0xe1f/red/3dprint/stl/led_connector_2x1_short.stl

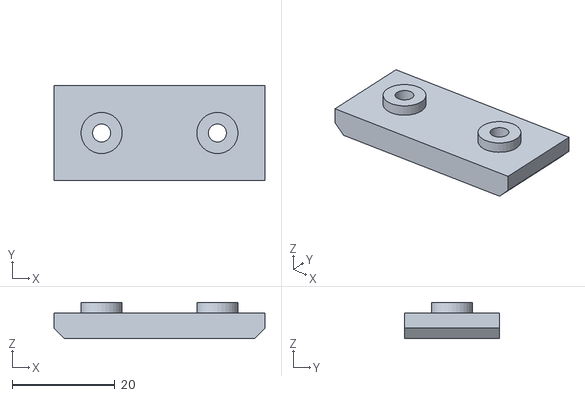
[picture p23: CAD file, 2024-03-31]
3dprint/stl/led_connector_2x1_short.stl
41.0 x 18.5 x 7.00
