0xe1f/red/3dprint/stl/ribbon_cable_clip.stl

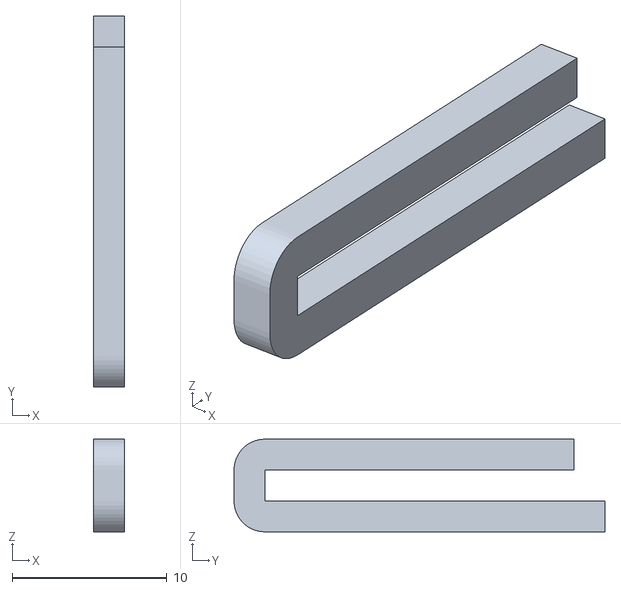
[picture p24: CAD file, 2024-03-31]
3dprint/stl/ribbon_cable_clip.stl
2.00 x 24.0 x 6.00
