0xe1f/red/pubsub/files.c

// Copyright (c) 2024 Akop Karapetyan
//
// Licensed under the Apache License, Version 2.0 (the "License");
// you may not use this file except in compliance with the License.
// You may obtain a copy of the License at
//
//    http://www.apache.org/licenses/LICENSE-2.0
//
// Unless required by applicable law or agreed to in writing, software
// distributed under the License is distributed on an "AS IS" BASIS,
// WITHOUT WARRANTIES OR CONDITIONS OF ANY KIND, either express or implied.
// See the License for the specific language governing permissions and
// limitations under the License.

#include <stdio.h>
#include <stdlib.h>
#include <string.h>
#include <sys/stat.h>
#include <unistd.h>
#include "unzip.h"
#include "un7z.h"
#include "libretro.h"
#include "server_args.h"
#include "log.h"
#include "files.h"

#define LOG_TAG "files"

static const char *preload_blocklist = "iso|cue|mp3|chd";
static const char *system_path_name = "bios";
static const char *save_path_name = "save";
static const char *recording_path_name = "rec";
static char system_path[1024];
static char save_path[1024];
static char recording_path[1024];
static char extracted_tempfile[1024] = {0};
static const char* get_filename(const char *path, bool include_ext);

extern struct retro_system_info system_info;
extern const struct retro_system_content_info_override *content_info;
extern struct retro_game_info *game_info;
extern struct retro_game_info_ext *game_info_ext;
extern ArgsOptions args;

static bool is_path_supported(const char *path, bool *need_fullpath);
static bool has_extension(const char *path, const char *ext);
static bool load_zip(const char *path);
static bool load_7z(const char *path);
static bool load_direct(const char *path);
static bool extension_one_of(const char *ext, const char *ext_delim);
static void copy_str(char *dst, size_t dst_size, const char *src);
static void copy_str_n(char *dst, size_t dst_size, const char *src, size_t n);
static void append_str(char *dst, size_t dst_size, const char *src);
static void join_dir(char *dst, size_t dst_size, const char *base, const char *name);
static void dirname_copy(char *dst, size_t dst_size, const char *path);
static void split_name_ext(const char *path, char *name, size_t name_size,
                           char *ext, size_t ext_size);

static void copy_str(char *dst, size_t dst_size, const char *src)
{
    if (dst_size == 0) {
        return;
    }
    if (!src) {
        dst[0] = '\0';
        return;
    }
    size_t n = strlen(src);
    if (n >= dst_size) {
        n = dst_size - 1;
    }
    memcpy(dst, src, n);
    dst[n] = '\0';
}

static void copy_str_n(char *dst, size_t dst_size, const char *src, size_t n)
{
    if (dst_size == 0) {
        return;
    }
    if (!src) {
        dst[0] = '\0';
        return;
    }
    size_t len = 0;
    while (len < n && src[len]) {
        len++;
    }
    if (len >= dst_size) {
        len = dst_size - 1;
    }
    memcpy(dst, src, len);
    dst[len] = '\0';
}

static void append_str(char *dst, size_t dst_size, const char *src)
{
    size_t used = strlen(dst);
    if (used < dst_size) {
        copy_str(dst + used, dst_size - used, src);
    }
}

static void join_dir(char *dst, size_t dst_size, const char *base, const char *name)
{
    size_t len = strlen(base);
    copy_str(dst, dst_size, base);
    if (len > 0 && base[len - 1] != '/') {
        append_str(dst, dst_size, "/");
    }
    append_str(dst, dst_size, name);
}

static void dirname_copy(char *dst, size_t dst_size, const char *path)
{
    const char *slash = strrchr(path, '/');
    if (slash) {
        copy_str_n(dst, dst_size, path, (size_t)(slash - path));
    } else {
        copy_str(dst, dst_size, ".");
    }
}

static void split_name_ext(const char *path, char *name, size_t name_size,
                           char *ext, size_t ext_size)
{
    const char *slash = strrchr(path, '/');
    copy_str(name, name_size, slash ? slash + 1 : path);
    ext[0] = '\0';
    char *dot = strrchr(name, '.');
    if (dot) {
        copy_str(ext, ext_size, dot + 1);
        *dot = '\0';
    }
}

static bool extension_one_of(const char *ext, const char *ext_delim)
{
    for (const char *p = ext_delim; *p; p++) {
        if (strncmp(p, ext, strlen(ext)) == 0 &&
            (*(p + strlen(ext)) == '|' || *(p + strlen(ext)) == '\0')) {
            return true;
        }
        // skip to next extension after pipe
        while (*p && *p != '|') p++;
    }
    return false;
}

static bool is_path_supported(const char *path, bool *need_fullpath)
{
    *need_fullpath = false;
    const char *ext = strrchr(path, '.');
    if (!ext) {
        log_w(LOG_TAG, "No file extension found: %s\n", path);
        return false;
    }
    ext++; // skip the dot

    for (const struct retro_system_content_info_override *info = content_info; info && info->extensions; info++) {
        if (extension_one_of(ext, info->extensions)) {
            *need_fullpath = info->need_fullpath;
            return true;
        }
    }

    if (system_info.valid_extensions && extension_one_of(ext, system_info.valid_extensions)) {
        *need_fullpath = system_info.need_fullpath;
        return true;
    }

    return false;
}

static bool has_extension(const char *path, const char *ext)
{
    const char *file_ext = strrchr(path, '.');
    return file_ext && strcasecmp(file_ext + 1, ext) == 0;
}

static bool load_zip(const char *path)
{
    static struct retro_game_info info_local;
    static struct retro_game_info_ext info_local_ext;
    info_local = (struct retro_game_info){ 0 };
    info_local_ext = (struct retro_game_info_ext){ 0 };
    extracted_tempfile[0] = '\0';

    unzFile fd = unzOpen(path);
    if (!fd) {
        log_e(LOG_TAG, "Failed to open zip: %s\n", path);
        return false;
    }

    static char archived_path[1024];
    static char archived_filename[512];
    static char archived_ext[512];
    static char dir[1024];
    void *data = NULL;
    archived_path[0] = '\0';
    archived_filename[0] = '\0';
    archived_ext[0] = '\0';
    dirname_copy(dir, sizeof(dir), path);

    unz_file_info info;
    bool need_fullpath = false;
    int ret = unzGoToFirstFile(fd);
    while (ret == UNZ_OK) {
        if (unzGetCurrentFileInfo(fd, &info, archived_path, sizeof(archived_path), 0, 0, 0, 0) == UNZ_OK) {
            if (is_path_supported(archived_path, &need_fullpath)) {
                if ((ret = unzOpenCurrentFile(fd)) == UNZ_OK) {
                    size_t size = info.uncompressed_size;
                    if (!(data = malloc(size))) {
                        log_e(LOG_TAG, "Failed to allocate %zu bytes for %s\n", size, archived_path);
                        unzCloseCurrentFile(fd);
                        continue;
                    }

                    if ((ret = unzReadCurrentFile(fd, data, size)) == (int) size) {
                        log_i(LOG_TAG, "Loaded '%s'\n", archived_path);

                        split_name_ext(archived_path, archived_filename, sizeof(archived_filename),
                                       archived_ext, sizeof(archived_ext));

                        if (need_fullpath) {
                            // Core needs a real file path - extract to a temp file
                            copy_str(extracted_tempfile, sizeof(extracted_tempfile), save_path);
                            append_str(extracted_tempfile, sizeof(extracted_tempfile), "/rom_XXXXXX");
                            int tmp_fd = mkstemp(extracted_tempfile);
                            FILE *tf = tmp_fd != -1 ? fdopen(tmp_fd, "wb") : NULL;
                            if (!tf) {
                                log_e(LOG_TAG, "Failed to create temp file in %s\n", save_path);
                                if (tmp_fd != -1) { close(tmp_fd); unlink(extracted_tempfile); }
                                extracted_tempfile[0] = '\0';
                                free(data);
                                data = NULL;
                                unzCloseCurrentFile(fd);
                                break;
                            }
                            fwrite(data, 1, size, tf);
                            fclose(tf);
                            free(data);
                            data = NULL;
                            size = 0;
                            info_local = (struct retro_game_info){ extracted_tempfile, NULL, 0, NULL };
                            info_local_ext = (struct retro_game_info_ext){
                                /* full_path */ extracted_tempfile,
                                /* archive_path */ path,
                                /* archive_file */ archived_path,
                                /* dir */ dir,
                                /* name */ archived_filename,
                                /* ext */ archived_ext,
                                /* meta */ NULL,
                                /* data */ NULL,
                                /* size */ 0,
                                /* file_in_archive */ true,
                                /* persistent_data */ true
                            };
                        } else {
                            info_local = (struct retro_game_info){ path, data, size, NULL };
                            info_local_ext = (struct retro_game_info_ext){
                                /* full_path */ NULL,
                                /* archive_path */ path,
                                /* archive_file */ archived_path,
                                /* dir */ dir,
                                /* name */ archived_filename,
                                /* ext */ archived_ext,
                                /* meta */ NULL,
                                /* data */ data,
                                /* size */ size,
                                /* file_in_archive */ true,
                                /* persistent_data */ true
                            };
                        }

                        unzCloseCurrentFile(fd);
                        break;
                    }

                    free(data);
                    unzCloseCurrentFile(fd);
                }
            }
        }
        ret = unzGoToNextFile(fd);
    }
    unzClose(fd);

    if (need_fullpath ? !(*extracted_tempfile) : !info_local.data) {
        log_w(LOG_TAG, "Nothing loaded from archive: %s\n", path);
        return false;
    }

    game_info = &info_local;
    game_info_ext = &info_local_ext;

    return true;
}

static bool load_7z(const char *path)
{
    static struct retro_game_info info_local;
    static struct retro_game_info_ext info_local_ext;
    info_local = (struct retro_game_info){ 0 };
    info_local_ext = (struct retro_game_info_ext){ 0 };
    extracted_tempfile[0] = '\0';

    _7z_file *z7 = NULL;
    _7z_error z7_err;

    z7_err = _7z_file_open(path, &z7);
    if (z7_err != _7ZERR_NONE) {
        return false;
    }

    static char archived_path[1024];
    static char archived_filename[512];
    static char archived_ext[512];
    static char dir[1024];
    archived_path[0] = '\0';
    archived_filename[0] = '\0';
    archived_ext[0] = '\0';
    dirname_copy(dir, sizeof(dir), path);

    unsigned short name_utf16[2048];
    bool need_fullpath = false;

    for (int i = 0, n = z7->db.NumFiles; i < n; i++) {
        size_t len = SzArEx_GetFileNameUtf16(&z7->db, i, NULL);
        size_t utf16_cap = sizeof(name_utf16) / sizeof(name_utf16[0]);
        if (len > utf16_cap) {
            log_e(LOG_TAG, "File name at index %d too long (%zu chars)\n", i, len);
            continue;
        }

        SzArEx_GetFileNameUtf16(&z7->db, i, name_utf16);
        size_t out = 0;
        size_t max = sizeof(archived_path) - 1;
        for (size_t j = 0; j < len && out < max; j++) {
            archived_path[out++] = (char)(name_utf16[j] & 0xff);
        }
        archived_path[out] = '\0';

        if (is_path_supported(archived_path, &need_fullpath)) {
            unsigned long size = SzArEx_GetFileSize(&z7->db, i);
            void *data = malloc(size);
            if (!data) {
                log_e(LOG_TAG, "Failed to allocate %zu bytes for %s\n", size, archived_path);
                continue;
            }

            z7->curr_file_idx = i;
            unsigned int wrote = 0;

            z7_err = _7z_file_decompress(z7, data, size, &wrote);
            if (z7_err != _7ZERR_NONE) {
                free(data);
                log_e(LOG_TAG, "Failed to decompress '%s' (err: %d)\n", archived_path, z7_err);
                continue;
            }

            unsigned int crc = crc32(0, (unsigned char *) data, wrote);
            if (crc != z7->db.CRCs.Vals[i]) {
                free(data);
                log_e(LOG_TAG, "CRC mismatch for '%s' (expected: %08x, got: %08x)\n",
                    archived_path, z7->db.CRCs.Vals[i], crc);
                continue;
            }

            split_name_ext(archived_path, archived_filename, sizeof(archived_filename),
                           archived_ext, sizeof(archived_ext));

            if (need_fullpath) {
                // Core needs a real file path - extract to a temp file
                copy_str(extracted_tempfile, sizeof(extracted_tempfile), save_path);
                append_str(extracted_tempfile, sizeof(extracted_tempfile), "/rom_XXXXXX");
                int tmp_fd = mkstemp(extracted_tempfile);
                FILE *tf = tmp_fd != -1 ? fdopen(tmp_fd, "wb") : NULL;
                if (!tf) {
                    log_e(LOG_TAG, "Failed to create temp file in %s\n", save_path);
                    if (tmp_fd != -1) { close(tmp_fd); unlink(extracted_tempfile); }
                    extracted_tempfile[0] = '\0';
                    free(data);
                    break;
                }
                fwrite(data, 1, size, tf);
                fclose(tf);
                free(data);
                info_local = (struct retro_game_info){ extracted_tempfile, NULL, 0, NULL };
                info_local_ext = (struct retro_game_info_ext){
                    /* full_path */ extracted_tempfile,
                    /* archive_path */ path,
                    /* archive_file */ archived_path,
                    /* dir */ dir,
                    /* name */ archived_filename,
                    /* ext */ archived_ext,
                    /* meta */ NULL,
                    /* data */ NULL,
                    /* size */ 0,
                    /* file_in_archive */ true,
                    /* persistent_data */ true
                };
            } else {
                info_local = (struct retro_game_info){ path, data, size, NULL };
                info_local_ext = (struct retro_game_info_ext){
                    /* full_path */ NULL,
                    /* archive_path */ path,
                    /* archive_file */ archived_path,
                    /* dir */ dir,
                    /* name */ archived_filename,
                    /* ext */ archived_ext,
                    /* meta */ NULL,
                    /* data */ data,
                    /* size */ size,
                    /* file_in_archive */ true,
                    /* persistent_data */ true
                };
            }

            break;
        }
    }

    _7z_file_close(z7);

    if (need_fullpath ? !(*extracted_tempfile) : !info_local.data) {
        log_w(LOG_TAG, "Nothing loaded from archive: %s\n", path);
        return false;
    }

    game_info = &info_local;
    game_info_ext = &info_local_ext;

    return true;
}

static bool load_direct(const char *path)
{
    static struct retro_game_info info_local;
    static struct retro_game_info_ext info_local_ext;
    info_local = (struct retro_game_info){ 0 };
    info_local_ext = (struct retro_game_info_ext){ 0 };

    static char dir[512];
    static char filename[512];
    static char ext[512];

    dirname_copy(dir, sizeof(dir), path);
    split_name_ext(path, filename, sizeof(filename), ext, sizeof(ext));

    void *data = NULL;
    size_t size = 0;
    bool preload = (!args.disable_preloading && !extension_one_of(ext, preload_blocklist))
        || args.force_preloading;
    log_d(LOG_TAG, "Preloading %s for '%s'\n", preload ? "enabled" : "disabled", path);

    if (preload) {
        FILE *f = fopen(path, "rb");
        if (!f) {
            log_e(LOG_TAG, "Failed to read file: %s\n", path);
            return false;
        }

        fseek(f, 0, SEEK_END);
        size = ftell(f);
        fseek(f, 0, SEEK_SET);

        data = malloc(size);
        if (!data) {
            log_e(LOG_TAG, "Failed to allocate %zu bytes for %s\n", size, path);
        } else {
            fread(data, 1, size, f);
        }
        fclose(f);
    }

    info_local = (struct retro_game_info){ path, data, size, NULL };
    info_local_ext = (struct retro_game_info_ext){
        /* full_path */ path,
        /* archive_path */ NULL,
        /* archive_file */ NULL,
        /* dir */ dir,
        /* name */ filename,
        /* ext */ ext,
        /* meta */ NULL,
        /* data */ data,
        /* size */ size,
        /* file_in_archive */ false,
        /* persistent_data */ true
    };

    if (preload && !info_local.data) {
        // preload failed
        log_e(LOG_TAG, "Preload failed\n");
        return false;
    }

    game_info = &info_local;
    game_info_ext = &info_local_ext;

    return true;
}

static const char* get_filename(const char *path, bool include_ext)
{
    static char filename[1024];
    const char *slash = strrchr(path, '/');
    copy_str(filename, sizeof(filename), slash ? slash + 1 : path);
    if (!include_ext) {
        char *dot = strrchr(filename, '.');
        if (dot) {
            *dot = '\0';
        }
    }
    return filename;
}

static void sram_path_for(char *dst, size_t dst_size, const char *rom_path)
{
    copy_str(dst, dst_size, save_path);
    append_str(dst, dst_size, "/");
    append_str(dst, dst_size, get_filename(rom_path, false));
    append_str(dst, dst_size, ".srm");
}

bool files_load(const char *path)
{
    bool need_fullpath = false;
    if (is_path_supported(path, &need_fullpath)) {
        return load_direct(path);
    } else if (has_extension(path, "7z")) {
        return load_7z(path);
    } else if (has_extension(path, "zip")) {
        return load_zip(path);
    } else {
        return false;
    }
}

void files_mkdirs(const char *base_path)
{
    join_dir(system_path, sizeof(system_path), base_path, system_path_name);
    join_dir(save_path, sizeof(save_path), base_path, save_path_name);
    join_dir(recording_path, sizeof(recording_path), base_path, recording_path_name);

    struct stat st = {0};
    if (stat(system_path, &st) == -1) {
        mkdir(system_path, 0755);
    }
    if (stat(save_path, &st) == -1) {
        mkdir(save_path, 0755);
    }
    if (stat(recording_path, &st) == -1) {
        mkdir(recording_path, 0755);
    }
}

void files_clean_up()
{
    if (game_info) {
        // data pointer is shared between game_info and game_info_ext
        free((void*)game_info->data);
        game_info = NULL;
        game_info_ext = NULL;
    }
    if (extracted_tempfile[0] != '\0') {
        unlink(extracted_tempfile);
        extracted_tempfile[0] = '\0';
    }
}

const char* files_system_path()
{
    return system_path;
}

const char* files_save_path()
{
    return save_path;
}

bool files_save_sram(const char *rom_path, const void *sram_data, size_t sram_size)
{
    char path[1024];
    sram_path_for(path, sizeof(path), rom_path);
    FILE *f = fopen(path, "wb");
    if (!f) {
        log_e(LOG_TAG, "Failed to save SRAM to '%s'\n", path);
        return false;
    }

    fwrite(sram_data, 1, sram_size, f);
    fclose(f);

    return true;
}

bool files_restore_sram(const char *rom_path, void *sram_data, size_t sram_size)
{
    char path[1024];
    sram_path_for(path, sizeof(path), rom_path);
    if (access(path, F_OK) == -1) {
        log_d(LOG_TAG, "No SRAM file for '%s'\n", path);
        return true;
    }

    FILE *f = fopen(path, "rb");
    if (!f) {
        log_e(LOG_TAG, "Couldn't read SRAM file from '%s'\n", path);
        return false;
    }

    fseek(f, 0, SEEK_END);
    size_t file_size = (size_t) ftell(f);
    fseek(f, 0, SEEK_SET);

    if (file_size > sram_size) {
        log_w(LOG_TAG, "File '%s' is larger than expected SRAM size (expected: %zu, got: %zu)\n",
            path, sram_size, file_size);
        fclose(f);
        return false;
    }

    size_t read = fread(sram_data, 1, file_size, f);
    fclose(f);

    if (read != file_size) {
        log_e(LOG_TAG, "Failed to read SRAM data from '%s' (expected: %zu, got: %zu)\n",
            path, file_size, read);
    } else {
        log_i(LOG_TAG, "Restored SRAM data from '%s' (size: %zu bytes)\n", path, read);
    }

    return read == file_size;
}

const char* files_rom_recording_path(const char *rom_path, uint32_t slot)
{
    static char path[1024];
    char tail[] = "_0.rec";
    tail[1] = (char)('0' + (slot > 9 ? 9 : slot));
    copy_str(path, sizeof(path), recording_path);
    append_str(path, sizeof(path), "/");
    append_str(path, sizeof(path), get_filename(rom_path, false));
    append_str(path, sizeof(path), tail);

    return path;
}
