0xe1f/red/pubsub/server_xm.c

// Copyright (c) 2024 Akop Karapetyan
//
// Licensed under the Apache License, Version 2.0 (the "License");
// you may not use this file except in compliance with the License.
// You may obtain a copy of the License at
//
//    http://www.apache.org/licenses/LICENSE-2.0
//
// Unless required by applicable law or agreed to in writing, software
// distributed under the License is distributed on an "AS IS" BASIS,
// WITHOUT WARRANTIES OR CONDITIONS OF ANY KIND, either express or implied.
// See the License for the specific language governing permissions and
// limitations under the License.

#include "server_xm.h"

#include <stdlib.h>
#include <string.h>
#include <nats/nats.h>
#include <lz4.h>
#include "pb_decode.h"
#include "log.h"
#include "subjects.h"

#define LOG_TAG "server_xm"

static natsConnection *conn = NULL;
static natsSubscription *sub = NULL;
static uint8_t *video_msg_buf      = NULL;
static size_t   video_msg_buf_size = 0;
static uint8_t *audio_msg_buf      = NULL;
static size_t   audio_msg_buf_size = 0;

void xm_init(const char *server_url)
{
    if (conn) {
        log_e(LOG_TAG, "NATS connection already initialized\n");
        return;
    }
    // Connect to NATS server
    natsOptions *opts;
    natsOptions_Create(&opts);

    natsStatus s;
    if ((s = natsOptions_SetMaxReconnect(opts, 50)) != NATS_OK) {
        log_e(LOG_TAG, "Error setting max reconnect: %s\n", natsStatus_GetText(s));
        natsOptions_Destroy(opts);
        return;
    }
    if ((s = natsOptions_SetReconnectWait(opts, 250)) != NATS_OK) {
        log_e(LOG_TAG, "Error setting reconnect wait: %s\n", natsStatus_GetText(s));
        natsOptions_Destroy(opts);
        return;
    }
    if ((s = natsOptions_SetRetryOnFailedConnect(opts, true, NULL, NULL)) != NATS_OK) {
        log_e(LOG_TAG, "Error setting retry on failed connect: %s\n", natsStatus_GetText(s));
        natsOptions_Destroy(opts);
        return;
    }
    if ((s = natsOptions_SetSendAsap(opts, true)) != NATS_OK) {
        log_e(LOG_TAG, "Error setting send asap: %s\n", natsStatus_GetText(s));
        natsOptions_Destroy(opts);
        return;
    }
    if ((s = natsOptions_SetURL(opts, server_url)) != NATS_OK) {
        log_e(LOG_TAG, "Error setting NATS server URL: %s\n", natsStatus_GetText(s));
        natsOptions_Destroy(opts);
        return;
    }

    s = natsConnection_Connect(&conn, opts);
    natsOptions_Destroy(opts);

    if (s != NATS_OK) {
        log_e(LOG_TAG, "Error connecting to NATS server: %s\n", natsStatus_GetText(s));
        return;
    }

    log_i(LOG_TAG, "Connected to NATS server at %s\n", server_url);
    log_i(LOG_TAG, "Will publish video frames to '%s'\n", SUBJECT_VIDEO_FRAMES);

    s = natsConnection_SubscribeSync(&sub, conn, SUBJECT_REQUESTS);
    if (s != NATS_OK) {
        log_e(LOG_TAG, "Error subscribing to requests '%s': %s\n",
            SUBJECT_REQUESTS, natsStatus_GetText(s));
        natsConnection_Destroy(conn);
        conn = NULL;
        return;
    }
}

void xm_poll_requests(const RequestHandler handler)
{
    if (!conn || !sub) {
        log_e(LOG_TAG, "NATS connection or subscription not initialized\n");
        return;
    }

    natsMsg *msg = NULL;
    natsStatus s = natsSubscription_NextMsg(&msg, sub, 0);

    if (s == NATS_OK) {
        const uint8_t *payload = (const uint8_t*)natsMsg_GetData(msg);
        int len = natsMsg_GetDataLength(msg);

        RequestEnvelope *env = request_envelope__unpack(NULL, len, payload);
        if (env) {
            const char *reply_inbox = natsMsg_GetReply(msg);
            if (reply_inbox && *reply_inbox) {
                ResponseEnvelope resp = RESPONSE_ENVELOPE__INIT;
                handler(env, &resp);

                size_t resp_len = response_envelope__get_packed_size(&resp);
                uint8_t *resp_buf = malloc(resp_len);
                if (resp_buf) {
                    response_envelope__pack(&resp, resp_buf);
                    natsConnection_Publish(conn, reply_inbox, resp_buf, (int) resp_len);
                    free(resp_buf);
                }
            }
            request_envelope__free_unpacked(env, NULL);
        }
        natsMsg_Destroy(msg);
        msg = NULL;
    } else if (s == NATS_TIMEOUT) {
        // Expected path 99% of the time: queue is empty, do nothing.
    } else {
        log_e(LOG_TAG, "NATS polling error: %s\n", natsStatus_GetText(s));
    }
}

void xm_publish_vid_frame(const VidFrameHeader *geometry, const void *content, size_t size)
{
    if (!conn) {
        log_e(LOG_TAG, "NATS connection not initialized\n");
        return;
    }

    // Ensure message buffer is large enough for header + worst-case compressed content
    int max_compressed = LZ4_compressBound(size);
    size_t needed = sizeof(VidFrameHeader) + max_compressed;
    if (needed > video_msg_buf_size) {
        free(video_msg_buf);
        video_msg_buf = malloc(needed);
        if (!video_msg_buf) {
            log_e(LOG_TAG, "Failed to allocate message buffer\n");
            video_msg_buf_size = 0;
            return;
        }
        video_msg_buf_size = needed;
    }

    // Write header, then compress pixel data directly into the remainder
    memcpy(video_msg_buf, geometry, sizeof(VidFrameHeader));
    int compressed_size = LZ4_compress_fast(
        (const char *)content,
        (char *)video_msg_buf + sizeof(VidFrameHeader),
        size, max_compressed, 4
    );
    if (compressed_size <= 0) {
        log_e(LOG_TAG, "LZ4 compression failed\n");
        return;
    }

    // Publish to NATS
    natsStatus s = natsConnection_Publish(conn,
        SUBJECT_VIDEO_FRAMES, video_msg_buf, sizeof(VidFrameHeader) + compressed_size);
    if (s != NATS_OK) {
        log_e(LOG_TAG, "Error publishing video frames to '%s': %s\n",
            SUBJECT_VIDEO_FRAMES, natsStatus_GetText(s));
    }
}

void xm_publish_aud_frame(const AudFrameHeader *header, const void *content, size_t size)
{
    if (!conn) {
        log_e(LOG_TAG, "NATS connection not initialized\n");
        return;
    }

    // Ensure message buffer is large enough for header + worst-case compressed content
    int max_compressed = LZ4_compressBound(size);
    size_t needed = sizeof(header) + max_compressed;
    if (needed > audio_msg_buf_size) {
        free(audio_msg_buf);
        audio_msg_buf = malloc(needed);
        if (!audio_msg_buf) {
            log_e(LOG_TAG, "Failed to allocate message buffer\n");
            audio_msg_buf_size = 0;
            return;
        }
        audio_msg_buf_size = needed;
    }

    // Write header, then compress pixel data directly into the remainder
    memcpy(audio_msg_buf, header, sizeof(AudFrameHeader));
    int compressed_size = LZ4_compress_fast(
        (const char *)content,
        (char *)audio_msg_buf + sizeof(AudFrameHeader),
        size, max_compressed, 4
    );
    if (compressed_size <= 0) {
        log_e(LOG_TAG, "LZ4 compression failed\n");
        return;
    }

    // Publish to NATS
    natsStatus s = natsConnection_Publish(conn,
        SUBJECT_AUDIO_FRAMES, audio_msg_buf, sizeof(AudFrameHeader) + compressed_size);
    if (s != NATS_OK) {
        log_e(LOG_TAG, "Error publishing audio frames to '%s': %s\n",
            SUBJECT_AUDIO_FRAMES, natsStatus_GetText(s));
    }
}

void xm_cleanup()
{
    if (sub) {
        natsSubscription_Destroy(sub);
        sub = NULL;
    }
    if (conn) {
        natsConnection_Destroy(conn);
        conn = NULL;
    }
    free(video_msg_buf);
    video_msg_buf = NULL;
    video_msg_buf_size = 0;
    free(audio_msg_buf);
    audio_msg_buf = NULL;
    audio_msg_buf_size = 0;
}
